Deshad/Aqua_Feed_Pi/images/Aqua_Soft.png

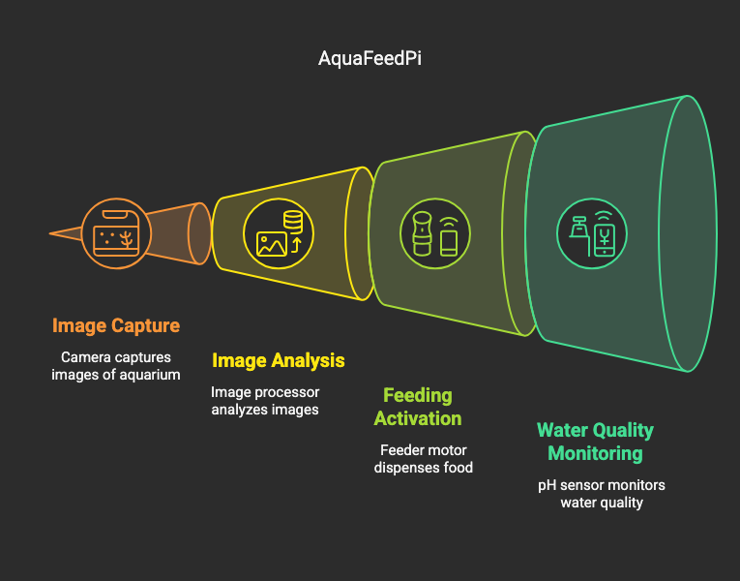
images/Aqua_Soft.png
