Deshad/Aqua_Feed_Pi/images/Bottom.jpg

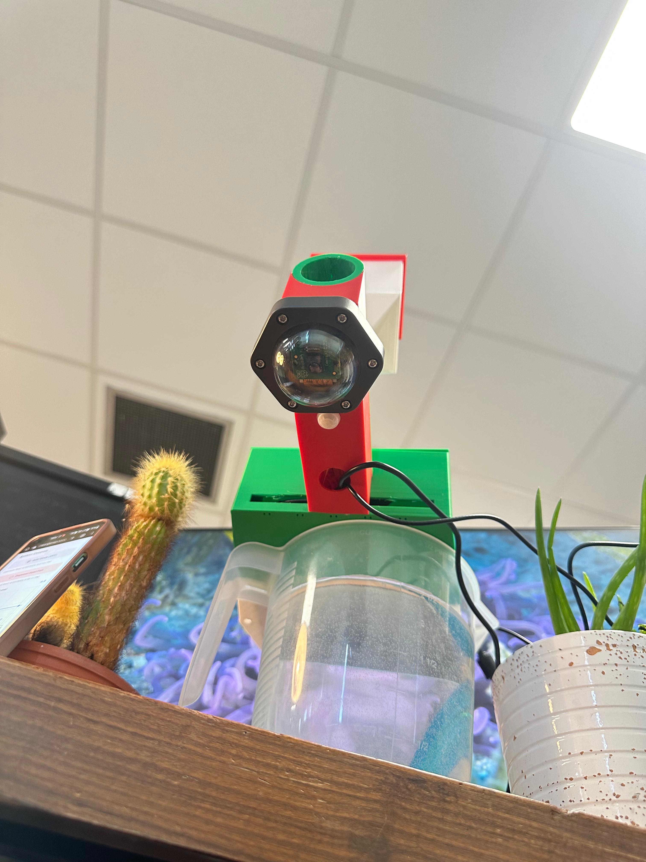
images/Bottom.jpg
