Deshad/Aqua_Feed_Pi/images/Left_Portrait.jpg

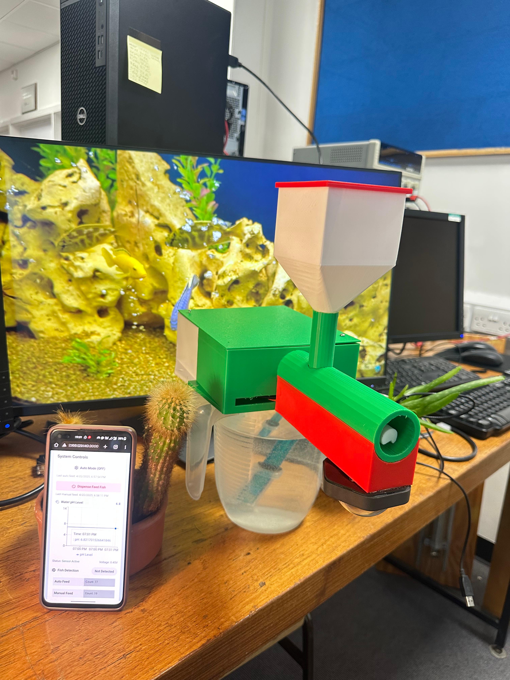
images/Left_Portrait.jpg
