Deshad/Aqua_Feed_Pi/images/Right_Landscape.jpg

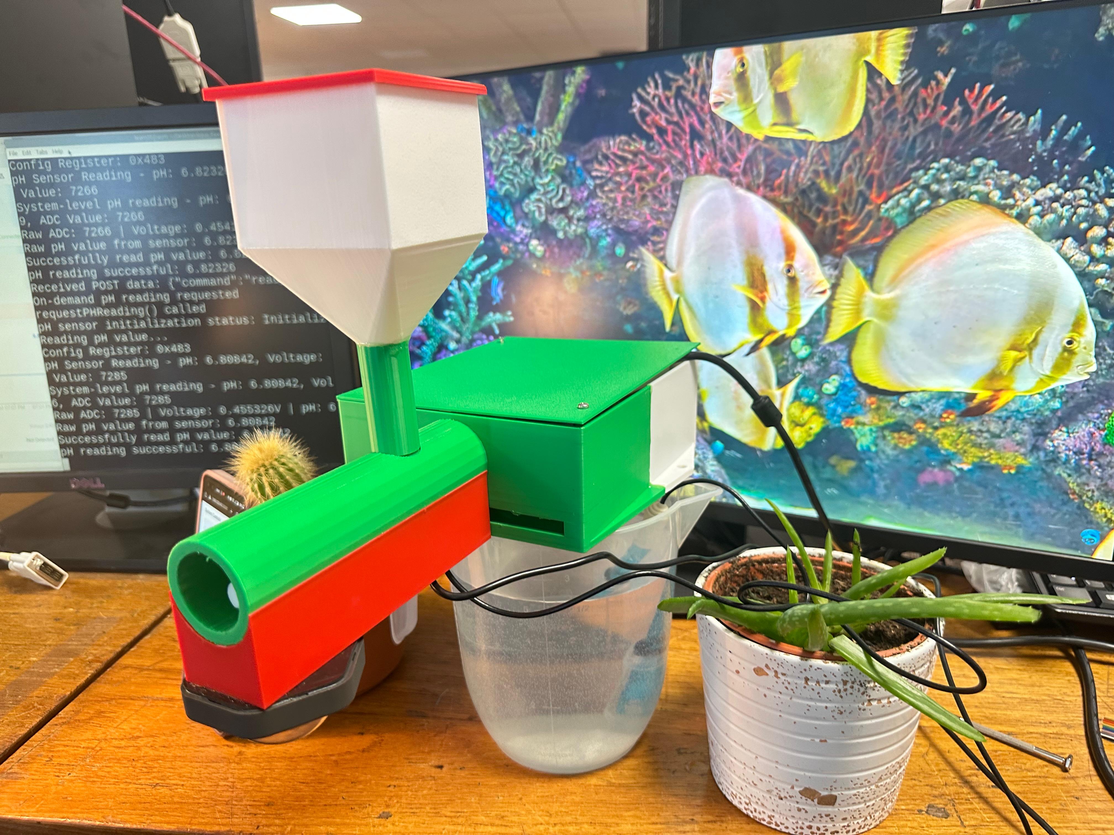
images/Right_Landscape.jpg
