Deshad/Aqua_Feed_Pi/images/Right_Potrait.jpg

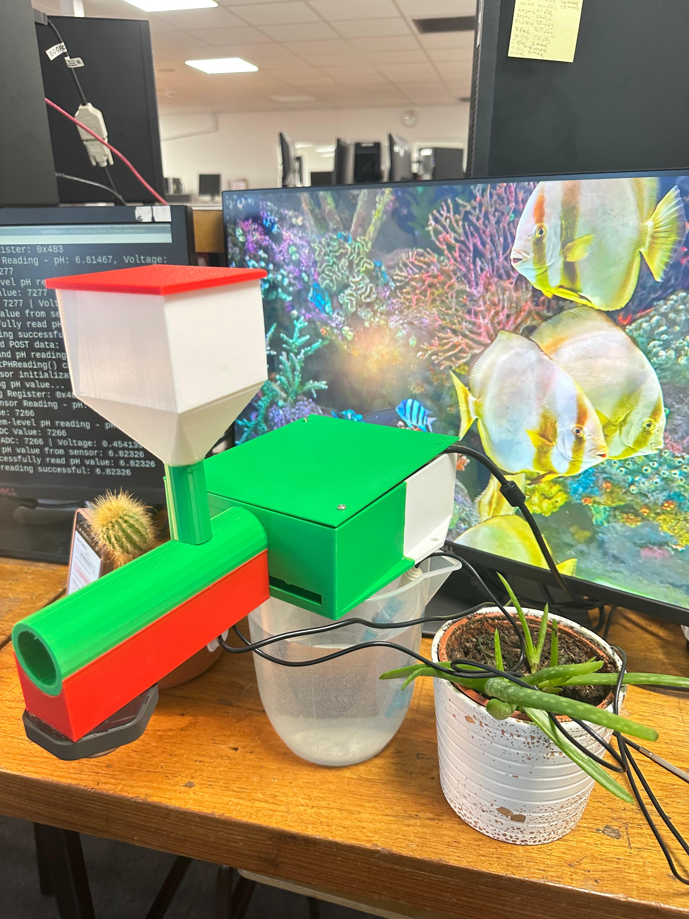
images/Right_Potrait.jpg
