Deshad/Aqua_Feed_Pi/images/Top_Left.jpg

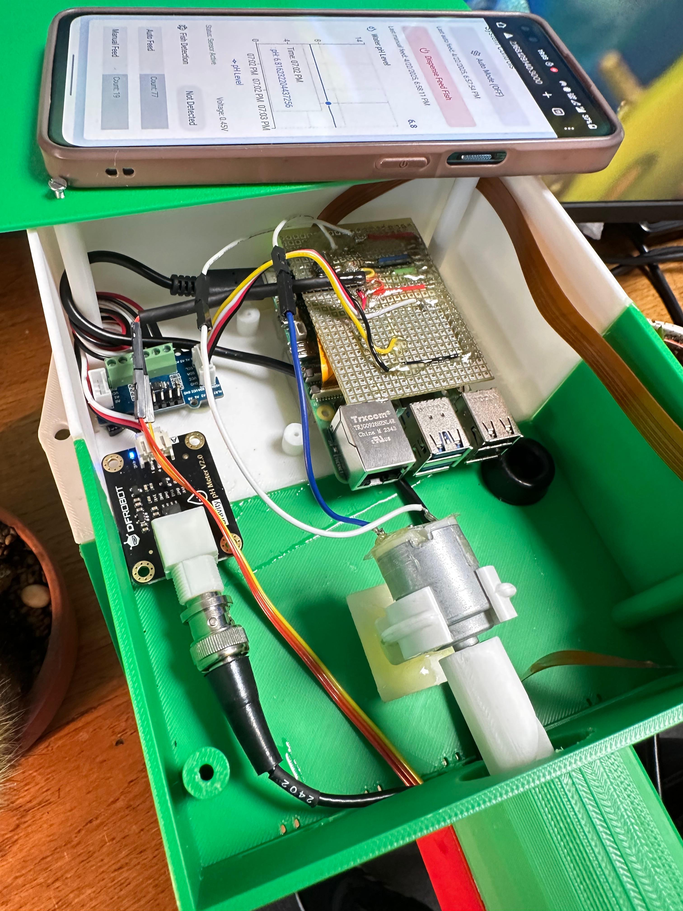
images/Top_Left.jpg
