Deshad/Aqua_Feed_Pi/images/Top_Right_Zoom.jpg

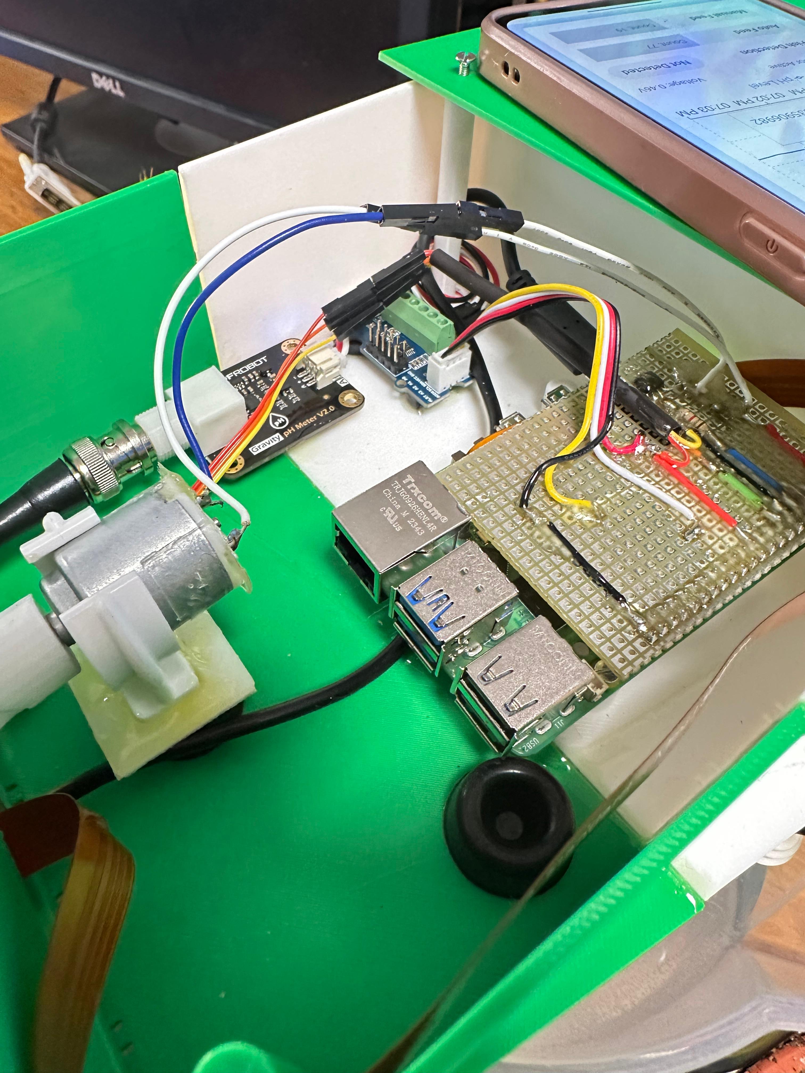
images/Top_Right_Zoom.jpg
