Deshad/Aqua_Feed_Pi/main_codes/src/fish_detection.jpg

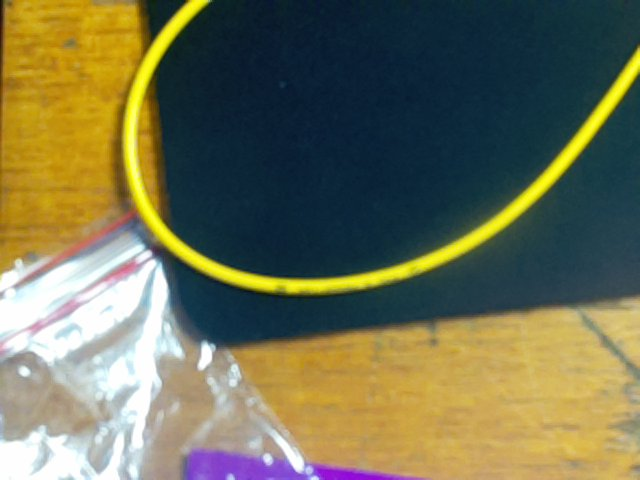
main_codes/src/fish_detection.jpg
