Deshad/Aqua_Feed_Pi/main_codes/build/fish_detection.jpg

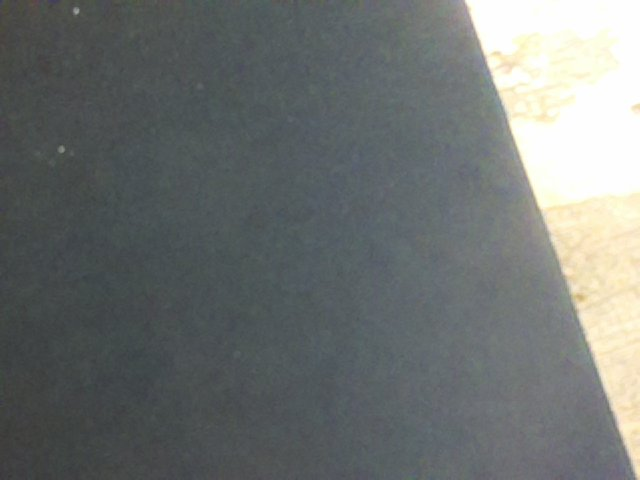
main_codes/build/fish_detection.jpg
