Deshad/Aqua_Feed_Pi/main_codes/build/last_detected_image.jpg

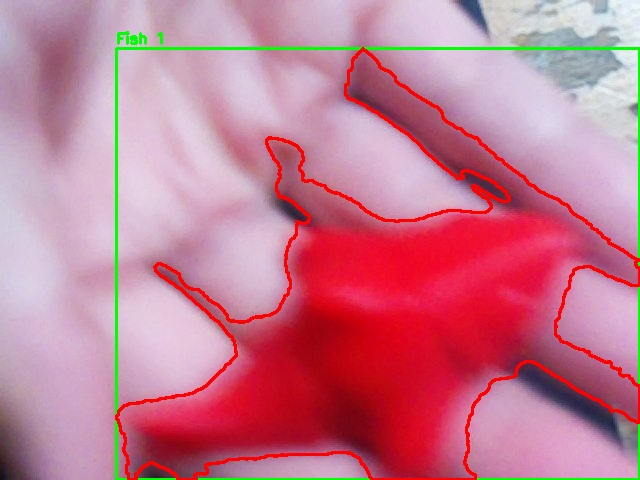
main_codes/build/last_detected_image.jpg
