Deshad/Aqua_Feed_Pi/main_codes/include/fish_monitoring_system.h

#ifndef FISH_MONITORING_SYSTEM_H
#define FISH_MONITORING_SYSTEM_H

#include "camera.h"
#include "feeder.h"
#include "image_processor.h"
#include "pir_sensor.h"
#include "fish_api.h"
#include "ph_sensor.h"
#include <memory>

/**
 * Main system class that connects all components
 */
class FishMonitoringSystem : public PirSensor::MotionCallbackInterface,
                             public PHSensor::PHSensorCallbackInterface {
public:
    FishMonitoringSystem();
    ~FishMonitoringSystem();
    
    // Start the system
    void start();
    
    // Stop the system
    void stop();
    
    // Motion detected callback ( MotionCallbackInterface)
    void motionDetected(gpiod_line_event e) override;
    // pH sample callback ( PHSensorCallbackInterface)
    void onPHSample(float pH, float voltage, int16_t adcValue) override;
    
private:
    void clearArchive();
    
    std::unique_ptr<PirSensor> m_pirSensor;
    std::unique_ptr<Camera> m_camera;
    std::unique_ptr<ImageProcessor> m_imageProcessor;
    std::unique_ptr<Feeder> m_feeder;
    std::unique_ptr<FishAPI> m_api;
    std::unique_ptr<PHSensor> m_phSensor;

};

#endif 
